AnasWagih25/Security_System_w_On-Edge_Facial_Recogniton/Code/Esp32CAM_Code/camera_index.h

//File: index_ov2640.html.gz, Size: 4316
#define index_ov2640_html_gz_len 4263
const uint8_t index_ov2640_html_gz[] = {
 0x1F, 0x8B, 0x08, 0x00, 0x1F, 0xF2, 0x36, 0x69, 0x02, 0xFF, 0xE5, 0x5D, 0x7B, 0x73, 0xD3, 0xC6,
 0x16, 0xFF, 0x3F, 0x9F, 0x42, 0x08, 0x2E, 0xB1, 0xA7, 0xB1, 0x63, 0x3B, 0x4E, 0x08, 0xC6, 0x16,
 0x17, 0x42, 0x80, 0xCE, 0xF0, 0x2A, 0x69, 0x69, 0x67, 0x3A, 0x1D, 0x58, 0x4B, 0x2B, 0x5B, 0x45,
 0x96, 0x54, 0x69, 0x65, 0x27, 0x65, 0xF2, 0x39, 0xEE, 0x07, 0xBA, 0x5F, 0xEC, 0x9E, 0x7D, 0x48,
 0x5A, 0xC9, 0x7A, 0xDA, 0xC5, 0xE6, 0xB6, 0xC9, 0x0C, 0x91, 0xAD, 0x3D, 0x67, 0xCF, 0x39, 0xBF,
 0xF3, 0xDA, 0xD5, 0x83, 0xF1, 0x1D, 0xC3, 0xD5, 0xC9, 0x8D, 0x87, 0x95, 0x39, 0x59, 0xD8, 0xDA,
 0xC1, 0x98, 0xFF, 0x51, 0xE0, 0x67, 0x3C, 0xC7, 0xC8, 0xE0, 0x87, 0xEC, 0xE3, 0x02, 0x13, 0xA4,
 0xE8, 0x73, 0xE4, 0x07, 0x98, 0x4C, 0xD4, 0x90, 0x98, 0x9D, 0x73, 0x35, 0x7B, 0xDA, 0x41, 0x0B,
 0x3C, 0x51, 0x97, 0x16, 0x5E, 0x79, 0xAE, 0x4F, 0x54, 0x45, 0x77, 0x1D, 0x82, 0x1D, 0x18, 0xBE,
 0xB2, 0x0C, 0x32, 0x9F, 0x18, 0x78, 0x69, 0xE9, 0xB8, 0xC3, 0x3E, 0x1C, 0x59, 0x8E, 0x45, 0x2C,
 0x64, 0x77, 0x02, 0x1D, 0xD9, 0x78, 0xD2, 0x97, 0x79, 0x11, 0x8B, 0xD8, 0x58, 0xBB, 0xBC, 0x7A,
 0x77, 0x32, 0x50, 0xDE, 0x7E, 0x18, 0x0C, 0xCF, 0x7A, 0xE3, 0x63, 0xFE, 0x5D, 0x32, 0x26, 0x20,
 0x37, 0xF2, 0x67, 0xFA, 0x33, 0x75, 0x8D, 0x1B, 0xE5, 0x4B, 0xEA, 0x2B, 0xFA, 0x63, 0x82, 0x10,
 0x1D, 0x13, 0x2D, 0x2C, 0xFB, 0x66, 0xA4, 0x3C, 0xF1, 0x61, 0xCE, 0xA3, 0x97, 0xD8, 0x5E, 0x62,
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
 0xF1, 0x2A, 0x83, 0x19, 0x37, 0xEC, 0xB6, 0x95, 0x8B, 0x5D, 0x30, 0x28, 0xC0, 0x10, 0xCA, 0xAC,
 0xD6, 0x80, 0xA1, 0xEB, 0xA5, 0xD2, 0x52, 0x68, 0x96, 0x6C, 0xA6, 0xD3, 0x08, 0xA6, 0xE9, 0x90,
 0x27, 0x9D, 0xA2, 0x82, 0xBA, 0xE9, 0xAA, 0x46, 0xB9, 0x83, 0xFF, 0x3A, 0xDB, 0x2C, 0x4D, 0x32,
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
};
